ste2425/PSP-Bluetooth/software/src/controllerManager.h

#pragma once

#include <Arduino.h>
#include <Bluepad32.h>
#include "led.h"
#include "PSPState.h"
#include "Mappings.h"
#include "timeout.h"
#include "interop.h"
#include "Settings.h"

void CTRMANAGER_loop();
void CTRMANAGER_setup();
void CTRMANAGER_enableConnections(bool enabled);
void CTRMANAGER_toggleConnections();
bool CTRMANAGER_newConnectionEnabled();
void CTRMANAGER_applyColours();
bool CTRMANAGER_pspBooting();
void CTRMANAGER_disconnectAll();
void CTRMANAGER_updateSettings();
bool CTRMANAGER_batteryLow();
void CTRMANAGER_bootConsole(bool bootOrEnd);
bool CTRMANAGER_isBooted();
