ste2425/PSP-Bluetooth/software/src/bt_service.gatt.h

// clang-format off
// ./bt_service.gatt.h generated from ./bt_service.gatt for BTstack
// it needs to be regenerated when the .gatt file is updated. 

// To generate ./bt_service.gatt.h:
// D:/code/bluepad32/external/btstack/tool/compile_gatt.py ./bt_service.gatt ./bt_service.gatt.h

// att db format version 1

// binary attribute representation:
// - size in bytes (16), flags(16), handle (16), uuid (16/128), value(...)

#include <stdint.h>

// Reference: https://en.cppreference.com/w/cpp/feature_test
#if __cplusplus >= 200704L
constexpr
#endif
const uint8_t profile_data[] =
{
    // ATT DB Version
    1,

    // 0x0001 PRIMARY_SERVICE-GAP_SERVICE
    0x0a, 0x00, 0x02, 0x00, 0x01, 0x00, 0x00, 0x28, 0x00, 0x18, 
    // 0x0002 CHARACTERISTIC-GAP_DEVICE_NAME - READ
    0x0d, 0x00, 0x02, 0x00, 0x02, 0x00, 0x03, 0x28, 0x02, 0x03, 0x00, 0x00, 0x2a, 
    // 0x0003 VALUE CHARACTERISTIC-GAP_DEVICE_NAME - READ -'Bluepad32'
    // READ_ANYBODY
    0x11, 0x00, 0x02, 0x00, 0x03, 0x00, 0x00, 0x2a, 0x42, 0x6c, 0x75, 0x65, 0x70, 0x61, 0x64, 0x33, 0x32, 
    // 0x0004 PRIMARY_SERVICE-GATT_SERVICE
    0x0a, 0x00, 0x02, 0x00, 0x04, 0x00, 0x00, 0x28, 0x01, 0x18, 
    // 0x0005 CHARACTERISTIC-GATT_DATABASE_HASH - READ
    0x0d, 0x00, 0x02, 0x00, 0x05, 0x00, 0x03, 0x28, 0x02, 0x06, 0x00, 0x2a, 0x2b, 
    // 0x0006 VALUE CHARACTERISTIC-GATT_DATABASE_HASH - READ -''
    // READ_ANYBODY
    0x18, 0x00, 0x02, 0x00, 0x06, 0x00, 0x2a, 0x2b, 0xe6, 0x60, 0xa7, 0x8f, 0x51, 0xd2, 0x5c, 0x9d, 0x52, 0x01, 0x12, 0x8e, 0xa6, 0xe8, 0x0e, 0x47, 
    //  Service
    // 0x0007 PRIMARY_SERVICE-4627C4A4-AC00-46B9-B688-AFC5C1BF7F63
    0x18, 0x00, 0x02, 0x00, 0x07, 0x00, 0x00, 0x28, 0x63, 0x7f, 0xbf, 0xc1, 0xc5, 0xaf, 0x88, 0xb6, 0xb9, 0x46, 0x00, 0xac, 0xa4, 0xc4, 0x27, 0x46, 
    // BT Characteristics
    // PSP Bluetooth Version
    // 0x0008 CHARACTERISTIC-4627C4A4-AC01-46B9-B688-AFC5C1BF7F63 - READ | DYNAMIC
    0x1b, 0x00, 0x02, 0x00, 0x08, 0x00, 0x03, 0x28, 0x02, 0x09, 0x00, 0x63, 0x7f, 0xbf, 0xc1, 0xc5, 0xaf, 0x88, 0xb6, 0xb9, 0x46, 0x01, 0xac, 0xa4, 0xc4, 0x27, 0x46, 
    // 0x0009 VALUE CHARACTERISTIC-4627C4A4-AC01-46B9-B688-AFC5C1BF7F63 - READ | DYNAMIC
    // READ_ANYBODY
    0x16, 0x00, 0x02, 0x03, 0x09, 0x00, 0x63, 0x7f, 0xbf, 0xc1, 0xc5, 0xaf, 0x88, 0xb6, 0xb9, 0x46, 0x01, 0xac, 0xa4, 0xc4, 0x27, 0x46, 
    // Controller Mappings
    // 0x000a CHARACTERISTIC-4627C4A4-AC02-46B9-B688-AFC5C1BF7F63 - READ | WRITE | DYNAMIC
    0x1b, 0x00, 0x02, 0x00, 0x0a, 0x00, 0x03, 0x28, 0x0a, 0x0b, 0x00, 0x63, 0x7f, 0xbf, 0xc1, 0xc5, 0xaf, 0x88, 0xb6, 0xb9, 0x46, 0x02, 0xac, 0xa4, 0xc4, 0x27, 0x46, 
    // 0x000b VALUE CHARACTERISTIC-4627C4A4-AC02-46B9-B688-AFC5C1BF7F63 - READ | WRITE | DYNAMIC
    // READ_ANYBODY, WRITE_ANYBODY
    0x16, 0x00, 0x0a, 0x03, 0x0b, 0x00, 0x63, 0x7f, 0xbf, 0xc1, 0xc5, 0xaf, 0x88, 0xb6, 0xb9, 0x46, 0x02, 0xac, 0xa4, 0xc4, 0x27, 0x46, 
    // Configuration Settings
    // 0x000c CHARACTERISTIC-4627C4A4-AC03-46B9-B688-AFC5C1BF7F63 - READ | WRITE | DYNAMIC
    0x1b, 0x00, 0x02, 0x00, 0x0c, 0x00, 0x03, 0x28, 0x0a, 0x0d, 0x00, 0x63, 0x7f, 0xbf, 0xc1, 0xc5, 0xaf, 0x88, 0xb6, 0xb9, 0x46, 0x03, 0xac, 0xa4, 0xc4, 0x27, 0x46, 
    // 0x000d VALUE CHARACTERISTIC-4627C4A4-AC03-46B9-B688-AFC5C1BF7F63 - READ | WRITE | DYNAMIC
    // READ_ANYBODY, WRITE_ANYBODY
    0x16, 0x00, 0x0a, 0x03, 0x0d, 0x00, 0x63, 0x7f, 0xbf, 0xc1, 0xc5, 0xaf, 0x88, 0xb6, 0xb9, 0x46, 0x03, 0xac, 0xa4, 0xc4, 0x27, 0x46, 
    // OTA - Commands
    // 0x000e CHARACTERISTIC-4627C4A4-AC04-46B9-B688-AFC5C1BF7F63 - WRITE | DYNAMIC
    0x1b, 0x00, 0x02, 0x00, 0x0e, 0x00, 0x03, 0x28, 0x08, 0x0f, 0x00, 0x63, 0x7f, 0xbf, 0xc1, 0xc5, 0xaf, 0x88, 0xb6, 0xb9, 0x46, 0x04, 0xac, 0xa4, 0xc4, 0x27, 0x46, 
    // 0x000f VALUE CHARACTERISTIC-4627C4A4-AC04-46B9-B688-AFC5C1BF7F63 - WRITE | DYNAMIC
    // WRITE_ANYBODY
    0x16, 0x00, 0x08, 0x03, 0x0f, 0x00, 0x63, 0x7f, 0xbf, 0xc1, 0xc5, 0xaf, 0x88, 0xb6, 0xb9, 0x46, 0x04, 0xac, 0xa4, 0xc4, 0x27, 0x46, 
    // OTA - Data
    // 0x0010 CHARACTERISTIC-4627C4A4-AC05-46B9-B688-AFC5C1BF7F63 - WRITE | DYNAMIC
    0x1b, 0x00, 0x02, 0x00, 0x10, 0x00, 0x03, 0x28, 0x08, 0x11, 0x00, 0x63, 0x7f, 0xbf, 0xc1, 0xc5, 0xaf, 0x88, 0xb6, 0xb9, 0x46, 0x05, 0xac, 0xa4, 0xc4, 0x27, 0x46, 
    // 0x0011 VALUE CHARACTERISTIC-4627C4A4-AC05-46B9-B688-AFC5C1BF7F63 - WRITE | DYNAMIC
    // WRITE_ANYBODY
    0x16, 0x00, 0x08, 0x03, 0x11, 0x00, 0x63, 0x7f, 0xbf, 0xc1, 0xc5, 0xaf, 0x88, 0xb6, 0xb9, 0x46, 0x05, 0xac, 0xa4, 0xc4, 0x27, 0x46, 
    // END
    0x00, 0x00, 
}; // total size 207 bytes 


//
// list service handle ranges
//
#define ATT_SERVICE_GAP_SERVICE_START_HANDLE 0x0001
#define ATT_SERVICE_GAP_SERVICE_END_HANDLE 0x0003
#define ATT_SERVICE_GAP_SERVICE_01_START_HANDLE 0x0001
#define ATT_SERVICE_GAP_SERVICE_01_END_HANDLE 0x0003
#define ATT_SERVICE_GATT_SERVICE_START_HANDLE 0x0004
#define ATT_SERVICE_GATT_SERVICE_END_HANDLE 0x0006
#define ATT_SERVICE_GATT_SERVICE_01_START_HANDLE 0x0004
#define ATT_SERVICE_GATT_SERVICE_01_END_HANDLE 0x0006
#define ATT_SERVICE_4627C4A4_AC00_46B9_B688_AFC5C1BF7F63_START_HANDLE 0x0007
#define ATT_SERVICE_4627C4A4_AC00_46B9_B688_AFC5C1BF7F63_END_HANDLE 0x0011
#define ATT_SERVICE_4627C4A4_AC00_46B9_B688_AFC5C1BF7F63_01_START_HANDLE 0x0007
#define ATT_SERVICE_4627C4A4_AC00_46B9_B688_AFC5C1BF7F63_01_END_HANDLE 0x0011

//
// list mapping between characteristics and handles
//
#define ATT_CHARACTERISTIC_GAP_DEVICE_NAME_01_VALUE_HANDLE 0x0003
#define ATT_CHARACTERISTIC_GATT_DATABASE_HASH_01_VALUE_HANDLE 0x0006
#define ATT_CHARACTERISTIC_4627C4A4_AC01_46B9_B688_AFC5C1BF7F63_01_VALUE_HANDLE 0x0009
#define ATT_CHARACTERISTIC_4627C4A4_AC02_46B9_B688_AFC5C1BF7F63_01_VALUE_HANDLE 0x000b
#define ATT_CHARACTERISTIC_4627C4A4_AC03_46B9_B688_AFC5C1BF7F63_01_VALUE_HANDLE 0x000d
#define ATT_CHARACTERISTIC_4627C4A4_AC04_46B9_B688_AFC5C1BF7F63_01_VALUE_HANDLE 0x000f
#define ATT_CHARACTERISTIC_4627C4A4_AC05_46B9_B688_AFC5C1BF7F63_01_VALUE_HANDLE 0x0011
