ste2425/PSP-Bluetooth/software/src/SettingsTypes.h

#ifndef SETTINGSTYPES_H
#define SETTINGSTYPES_H

#include <Arduino.h>

struct Settings {
  uint16_t ledBrightness;
  uint16_t throttleThreshold;
  uint16_t analogThreshold;
  uint16_t diagonalThreshold;
  uint16_t screenDelay;
  uint16_t coldBootDelay;
  uint16_t warmBootDelay;
  uint16_t shutdownDelay;
  uint16_t batteryWarning;
  bool useExtraCombo;
  bool useAlternativeShutdown;
  uint16_t clickMode; // 0 - nothing, 1 - controller pair, 2 - ble mode, 3 - toggle power
  uint16_t dblClickMode;
  uint16_t lngClickMode;
};

#endif
