ste2425/PSP-Bluetooth/mappings.h

#ifndef MAPPINGS_H
#define MAPPINGS_H

#include <Arduino.h>
#include "pspPins.h"
#include "controller.h"

struct pinMap {
  const byte pin;
  const int controllerMask;
  const CTR_accessorType type;
};

extern pinMap *MAPPINGS_pins;
extern uint8_t MAPPINGS_pin_size;

void MAPPINGS_next_mapping();

#endif
